jeanot1314/Hygie/software/2.0_HC-06_Serial_Exemple/UNO_HC/UNO_HC.ino

#include <SoftwareSerial.h>

SoftwareSerial hc06(2,3); // RXPIN TXPIN

void setup(){
  //Initialize Serial Monitor
  Serial.begin(9600);
  Serial.println("ENTER AT Commands:");
  //Initialize Bluetooth Serial Port
  hc06.begin(9600);
}

void loop(){
  //Write data from HC06 to Serial Monitor
  if (hc06.available()){
    Serial.print(hc06.read());
  }
  
  //Write from Serial Monitor to HC06
  if (Serial.available()){
    hc06.write(Serial.read());
  }  
}
